abaffa/Minimal-Terminal/_images/IMG_20220729_091114742.jpg

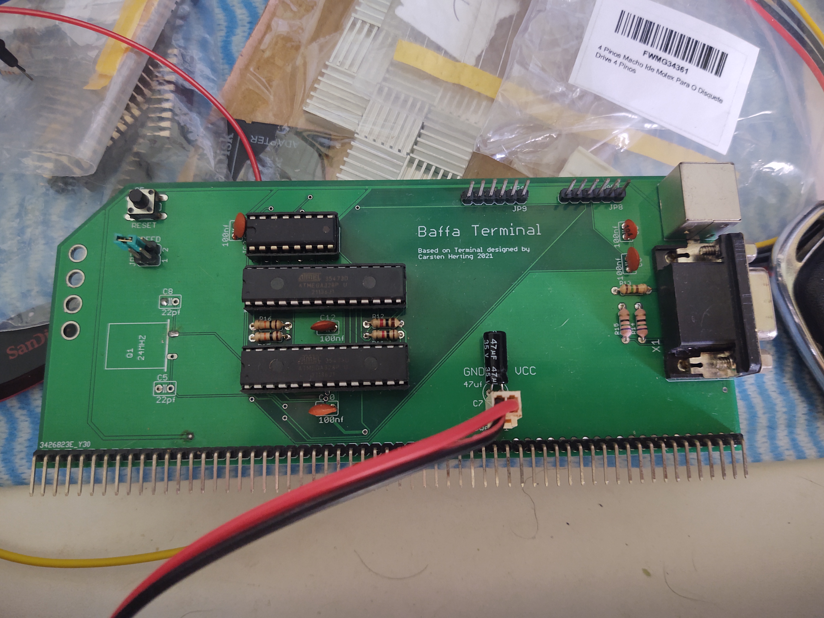
_images/IMG_20220729_091114742.jpg
