abaffa/Minimal-Terminal/_images/IMG_20220729_091138734.jpg

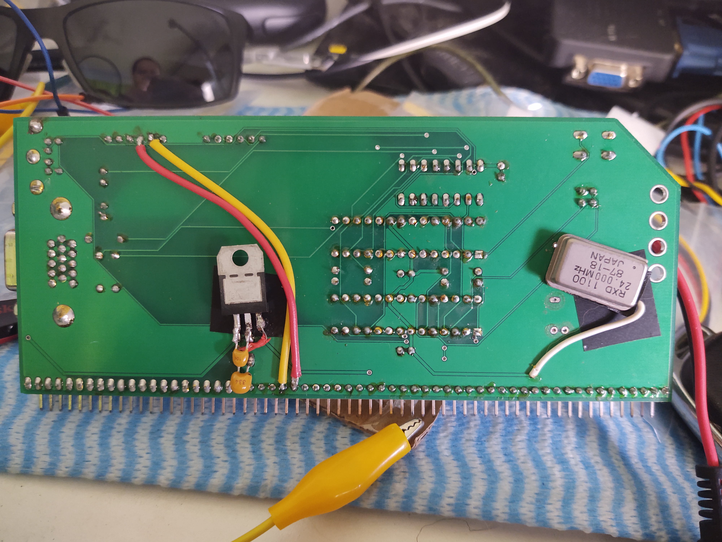
_images/IMG_20220729_091138734.jpg
